alexandrefelipemuller/powerfool/powerfool/display.h

unsigned char currentMenu = EEPROM.read(28);
unsigned char lap = 0;
unsigned long lastLap, startLap=0;
unsigned long bestLap=-1;
void changeMenu();
void setMenu();
void refreshMenu(inputFreq injectorInput, inputFreq speedInput, float consumption, float volts, int sensorPressureVal);
byte degreeSymbol[] = {
  B00000,
  B01110,
  B01010,
  B01110,
  B00000,
  B00000,
  B00000,
  B00000
};
